clauscarste/quadruped/stl_files/Leg/l1.stl

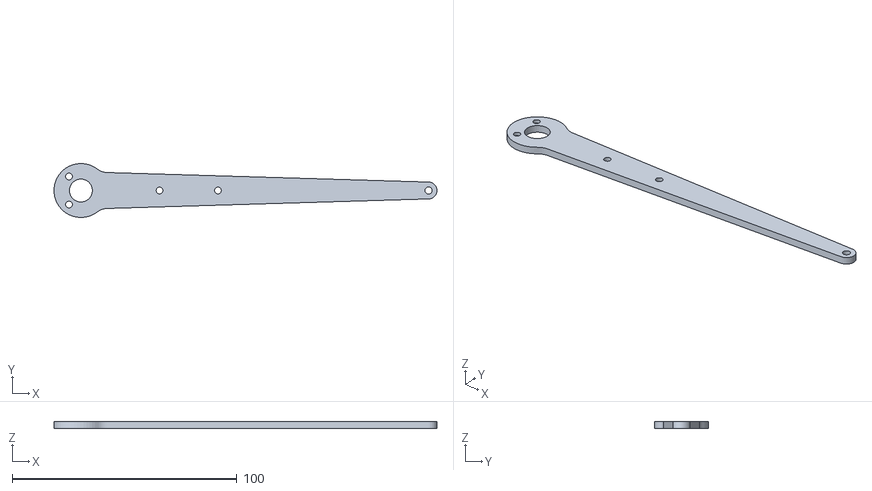
[picture p14: CAD file, 2022-11-11]
stl_files/Leg/l1.stl
170.5 x 24.0 x 3.00
