clauscarste/quadruped/stl_files/Main Body/m5.stl

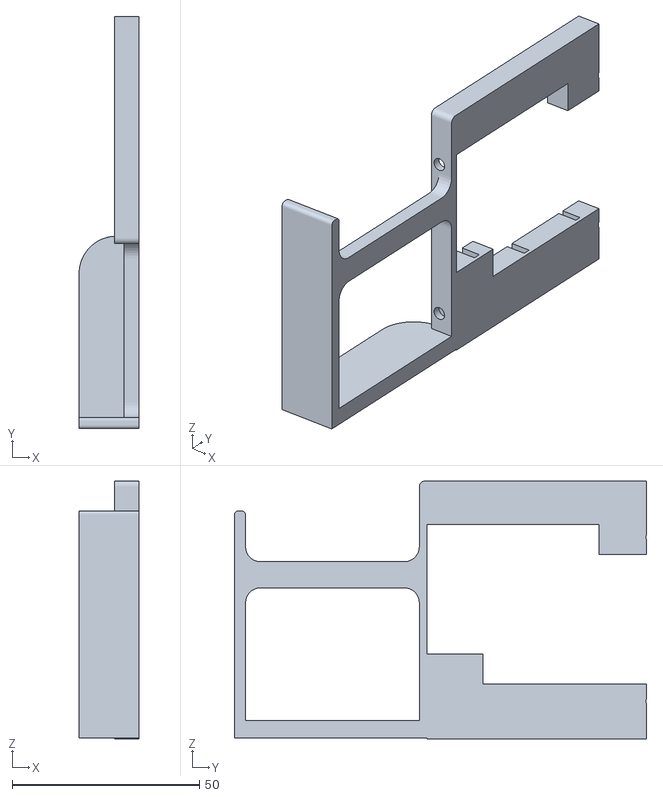
[picture p15: CAD file, 2022-11-11]
stl_files/Main Body/m5.stl
16.0 x 110.1 x 68.9
