clauscarste/quadruped/stl_files/Spine/s10.stl

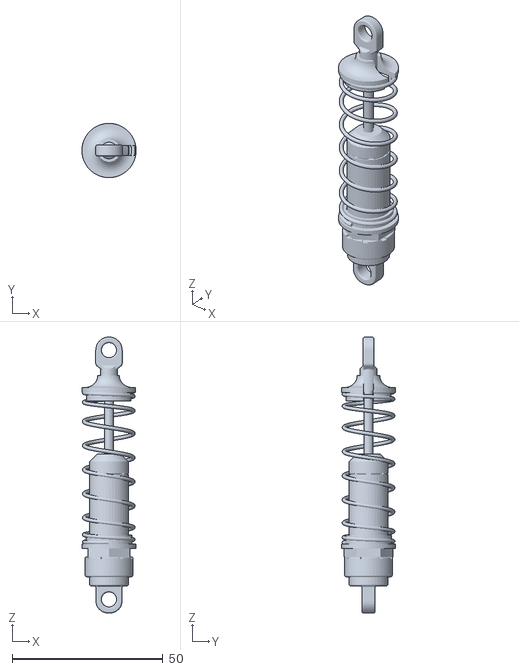
[picture p16: CAD file, 2022-11-11]
stl_files/Spine/s10.stl
18.0 x 18.0 x 91.5
