clauscarste/quadruped/control and simulation/simulation_files/simulation_test/full_quadruped_simulation_pos_control/meshes/lower_leg.stl

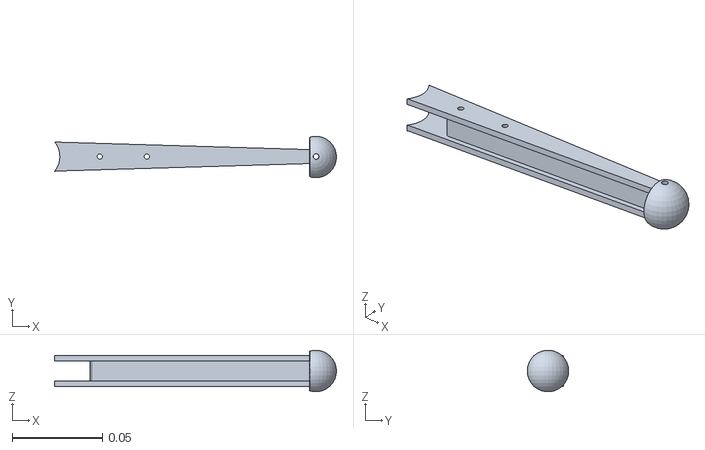
[picture p17: CAD file, 2023-01-09]
control and simulation/simulation_files/simulation_test/full_quadruped_simulation_pos_control/meshes/lower_leg.stl
0.156 x 0.023 x 0.0229
