clauscarste/quadruped/control and simulation/simulation_files/simulation_test/leg_only_simplided copy/meshes2/gearbox_1.stl

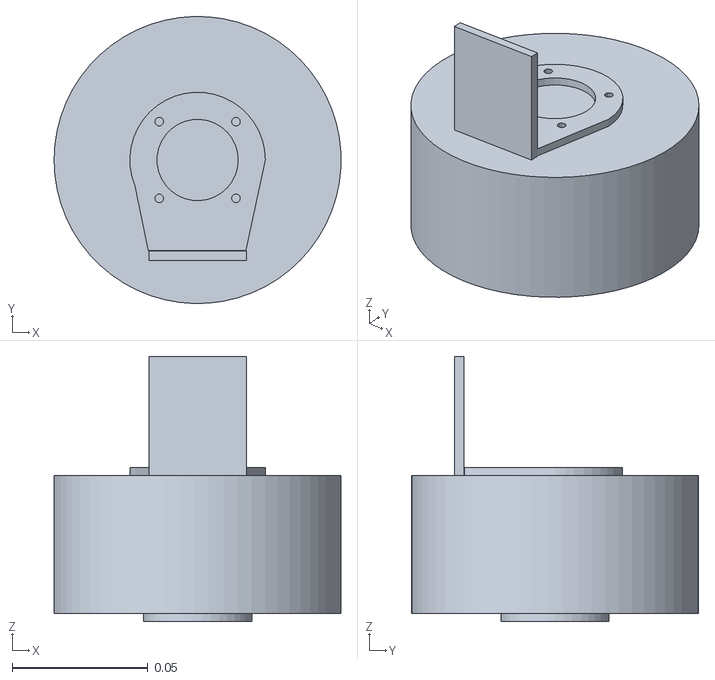
[picture p18: CAD file, 2023-01-24]
control and simulation/simulation_files/simulation_test/leg_only_simplided copy/meshes2/gearbox_1.stl
0.106 x 0.106 x 0.0978
