clauscarste/quadruped/stl_files/Gearbox/g8.stl

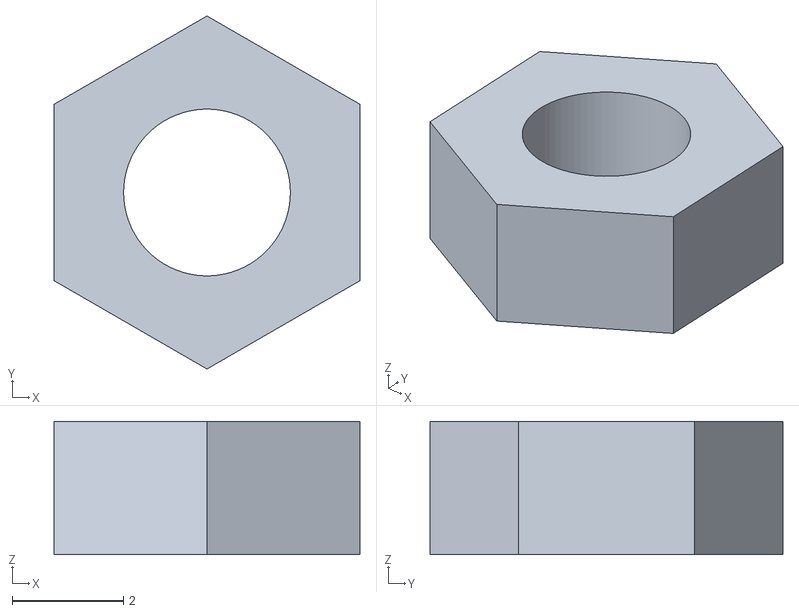
[picture p19: CAD file, 2022-11-11]
stl_files/Gearbox/g8.stl
5.50 x 6.35 x 2.40
