clauscarste/quadruped/stl_files/Main Body/m15.stl

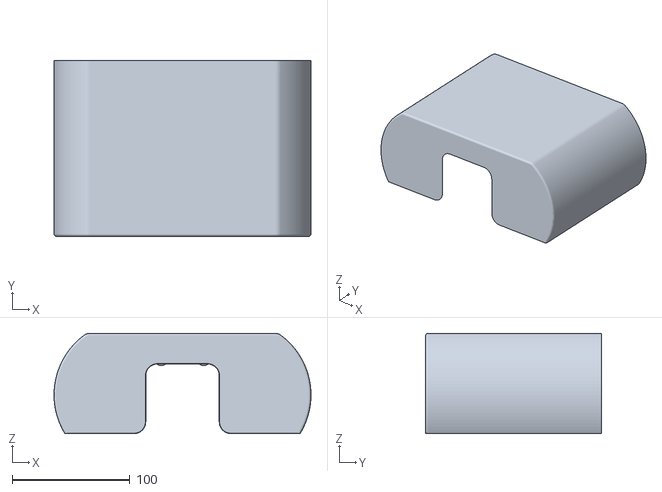
[picture p20: CAD file, 2022-11-11]
stl_files/Main Body/m15.stl
217.9 x 149.0 x 85.1
