clauscarste/quadruped/stl_files/Spine/s2.stl

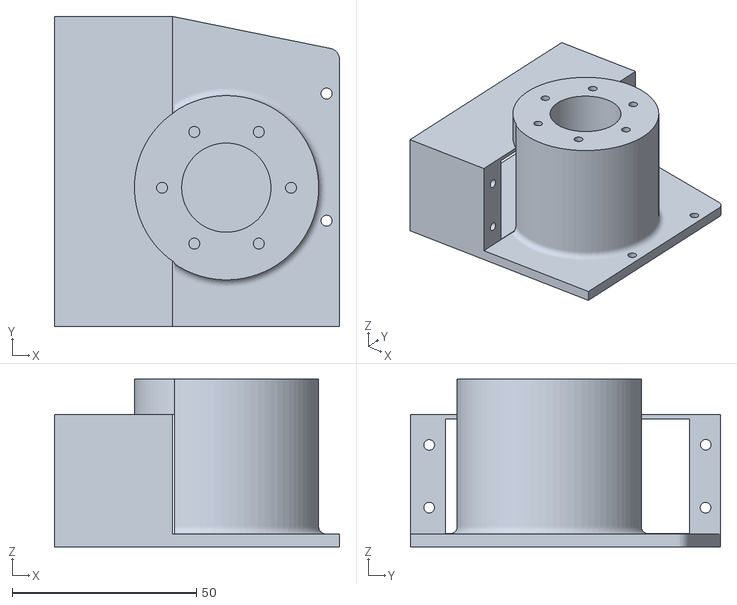
[picture p21: CAD file, 2022-11-11]
stl_files/Spine/s2.stl
77.3 x 84.2 x 45.5
