clauscarste/quadruped/control and simulation/simulation_files/simulation_test/full_quadruped_simulation_pos_control/meshes/case1.stl

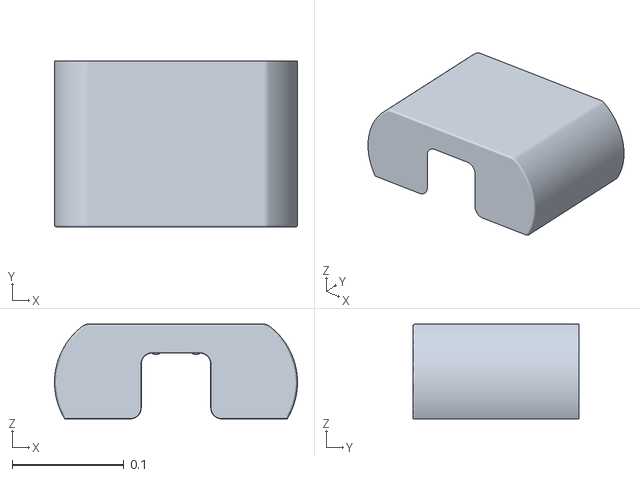
[picture p22: CAD file, 2022-11-25]
control and simulation/simulation_files/simulation_test/full_quadruped_simulation_pos_control/meshes/case1.stl
0.218 x 0.149 x 0.0851
