clauscarste/quadruped/stl_files/Gearbox/g6.stl

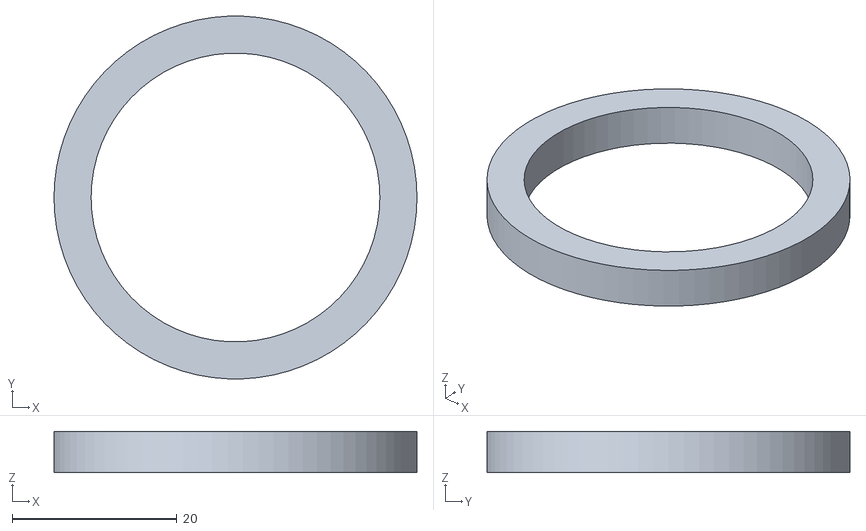
[picture p23: CAD file, 2022-11-11]
stl_files/Gearbox/g6.stl
44.0 x 44.0 x 5.00
