clauscarste/quadruped/stl_files/Leg/s4.stl

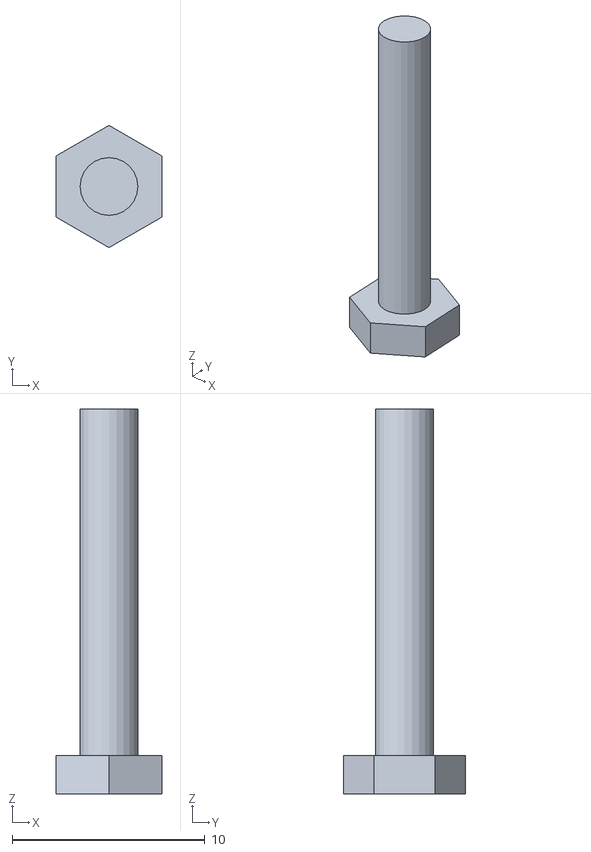
[picture p24: CAD file, 2022-11-11]
stl_files/Leg/s4.stl
5.50 x 6.35 x 20.0
