clauscarste/quadruped/stl_files/Main Body/m2.stl

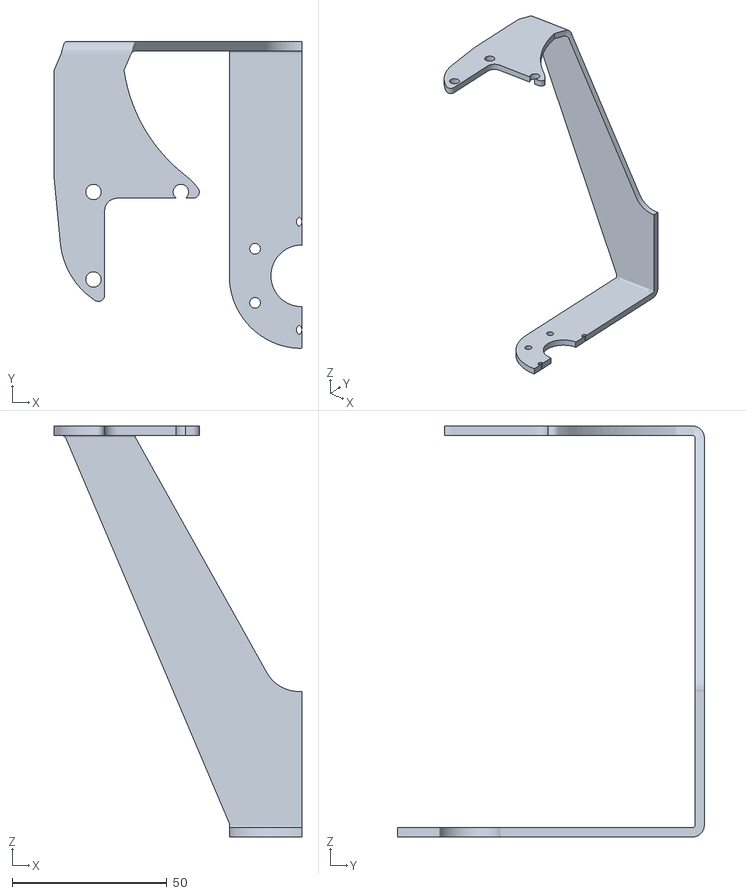
[picture p25: CAD file, 2022-11-11]
stl_files/Main Body/m2.stl
80.2 x 99.3 x 133.0
