clauscarste/quadruped/stl_files/Spine/s1.stl

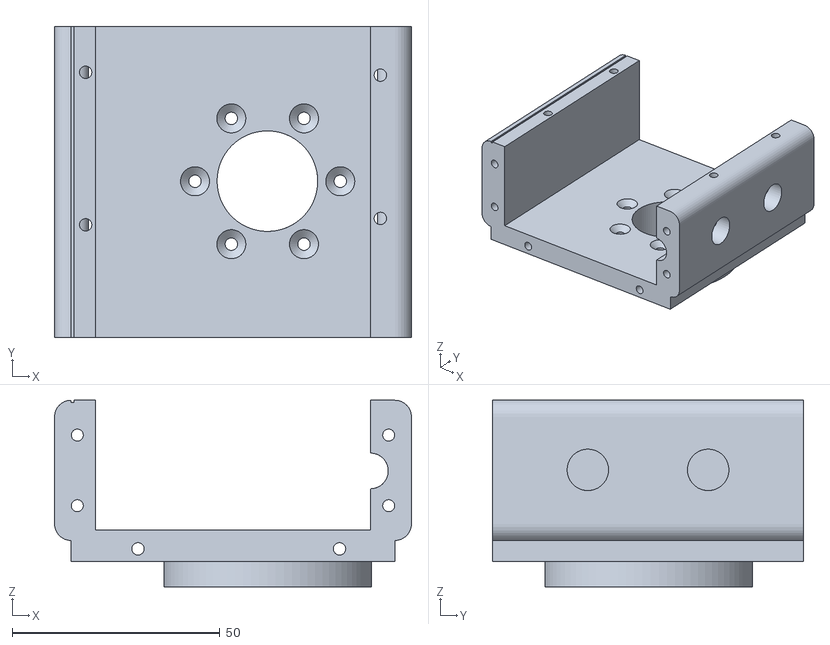
[picture p26: CAD file, 2022-11-11]
stl_files/Spine/s1.stl
86.0 x 75.0 x 44.9
