clauscarste/quadruped/control and simulation/simulation_files/simulation_test/full_quadruped_simulation_pos_control/meshes/case2.stl

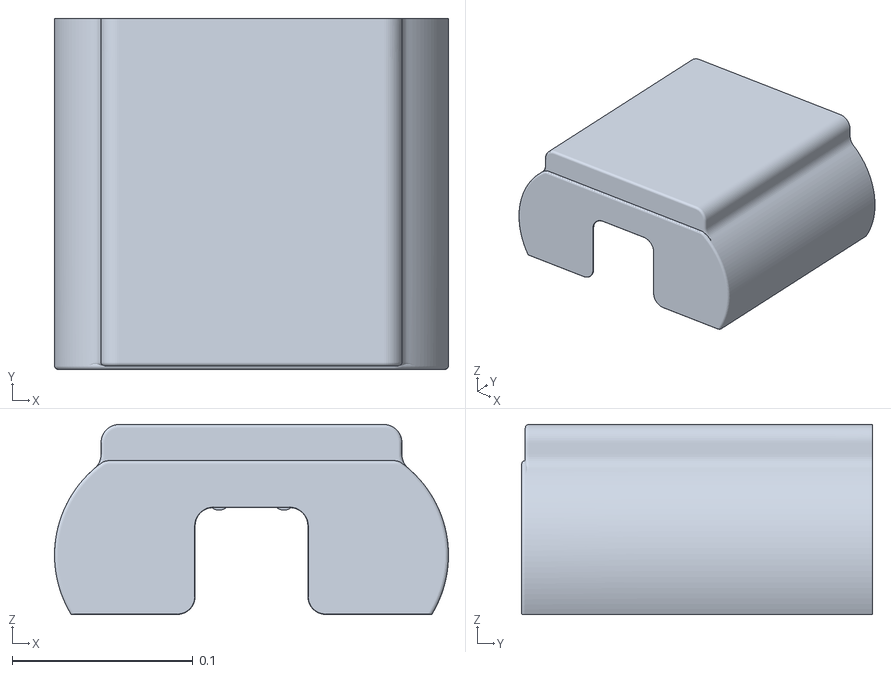
[picture p27: CAD file, 2022-11-25]
control and simulation/simulation_files/simulation_test/full_quadruped_simulation_pos_control/meshes/case2.stl
0.218 x 0.194 x 0.105
