clauscarste/quadruped/control and simulation/simulation_files/simulation_test/leg_only_simplided copy/meshes2/upper_leg.stl

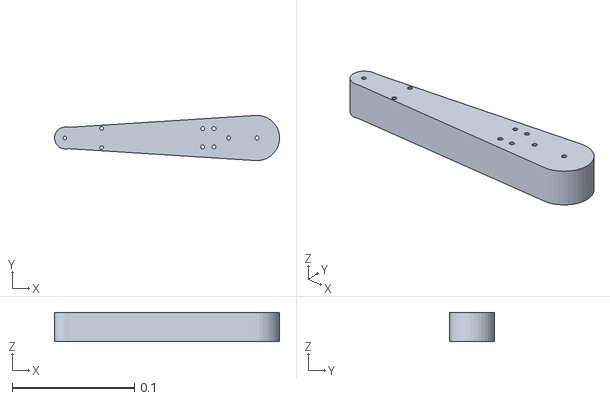
[picture p28: CAD file, 2023-01-24]
control and simulation/simulation_files/simulation_test/leg_only_simplided copy/meshes2/upper_leg.stl
0.184 x 0.0369 x 0.024
