clauscarste/quadruped/stl_files/Gearbox/g7.stl

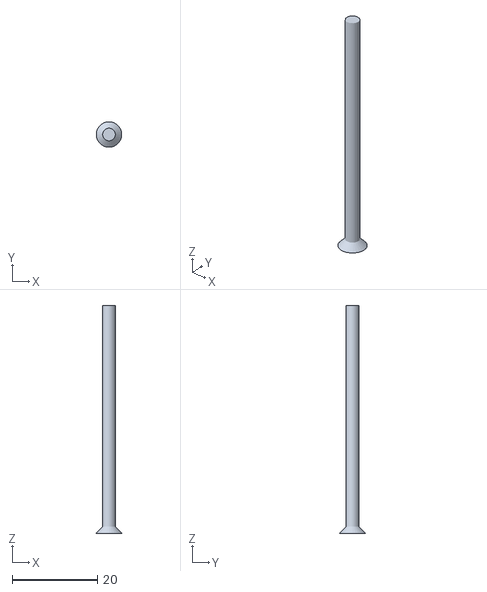
[picture p29: CAD file, 2022-11-11]
stl_files/Gearbox/g7.stl
6.00 x 6.00 x 53.6
