clauscarste/quadruped/stl_files/Leg/l3.stl

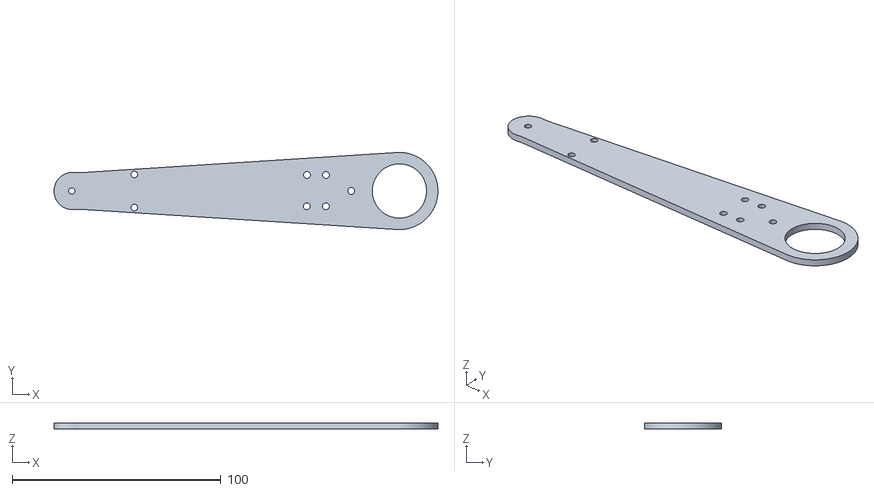
[picture p30: CAD file, 2022-11-11]
stl_files/Leg/l3.stl
184.1 x 37.0 x 3.00
