clauscarste/quadruped/stl_files/Main Body/m16.stl

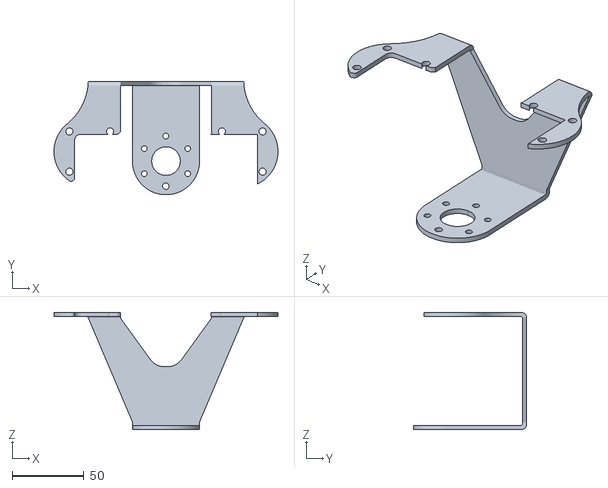
[picture p31: CAD file, 2022-11-11]
stl_files/Main Body/m16.stl
156.6 x 79.3 x 81.9
