clauscarste/quadruped/stl_files/Spine/s9.stl

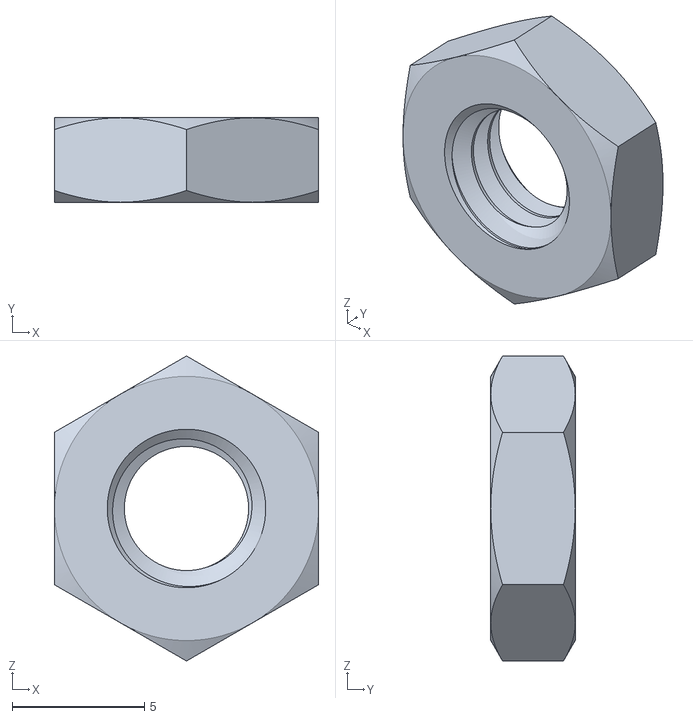
[picture p32: CAD file, 2022-11-11]
stl_files/Spine/s9.stl
10.0 x 3.20 x 11.5
