clauscarste/quadruped/control and simulation/simulation_files/simulation_test/full_quadruped_simulation_pos_control/meshes/front_alu_3.stl

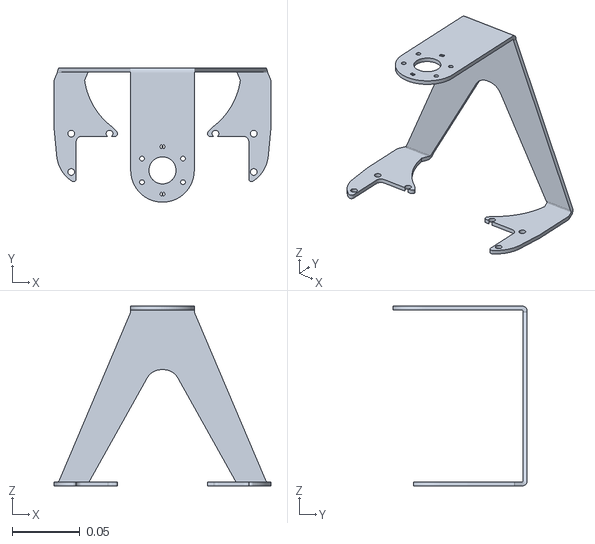
[picture p33: CAD file, 2022-11-15]
control and simulation/simulation_files/simulation_test/full_quadruped_simulation_pos_control/meshes/front_alu_3.stl
0.16 x 0.0993 x 0.133
