clauscarste/quadruped/control and simulation/simulation_files/simulation_test/leg_only_simplided copy/meshes/front_alu_1.stl

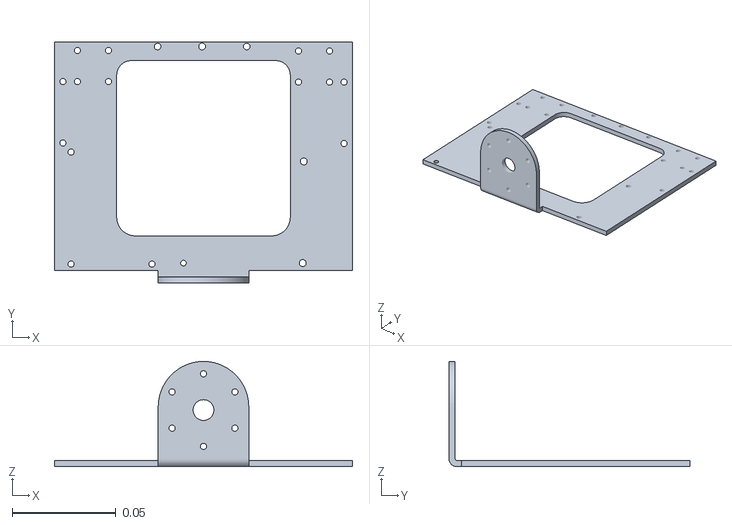
[picture p34: CAD file, 2022-11-15]
control and simulation/simulation_files/simulation_test/leg_only_simplided copy/meshes/front_alu_1.stl
0.144 x 0.116 x 0.0508
