clauscarste/quadruped/control and simulation/simulation_files/simulation_test/leg_only_simplided copy/meshes2/gearbox2.stl

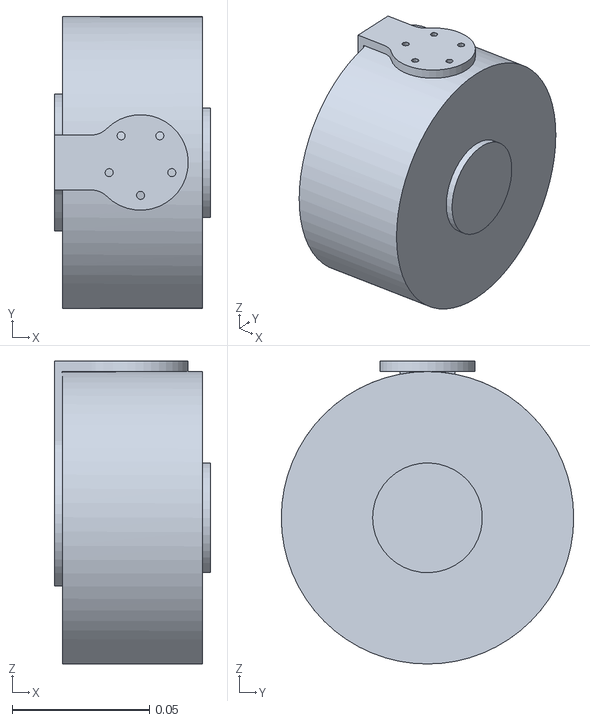
[picture p35: CAD file, 2023-01-24]
control and simulation/simulation_files/simulation_test/leg_only_simplided copy/meshes2/gearbox2.stl
0.0569 x 0.107 x 0.11
