clauscarste/quadruped/stl_files/Gearbox/g5.stl

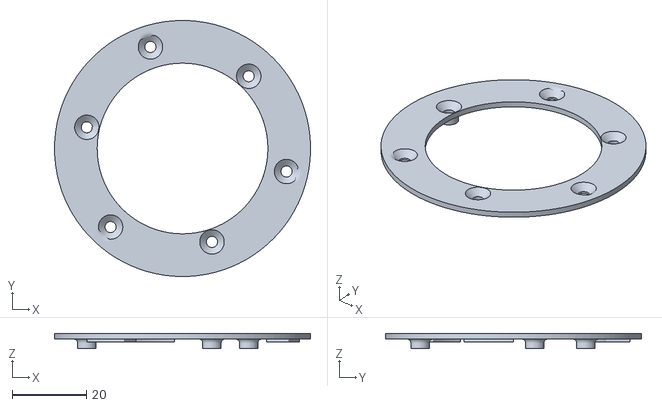
[picture p36: CAD file, 2022-11-11]
stl_files/Gearbox/g5.stl
69.0 x 69.0 x 4.00
