clauscarste/quadruped/stl_files/Leg/l2.stl

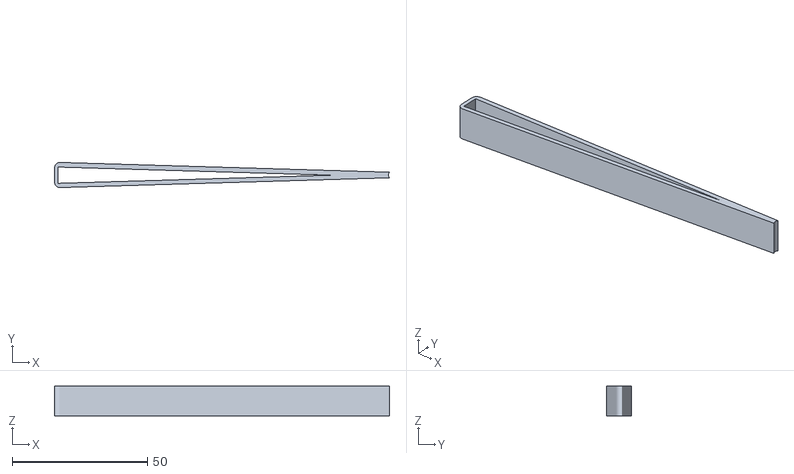
[picture p37: CAD file, 2022-11-11]
stl_files/Leg/l2.stl
124.1 x 9.31 x 11.0
