clauscarste/quadruped/stl_files/Main Body/m10.stl

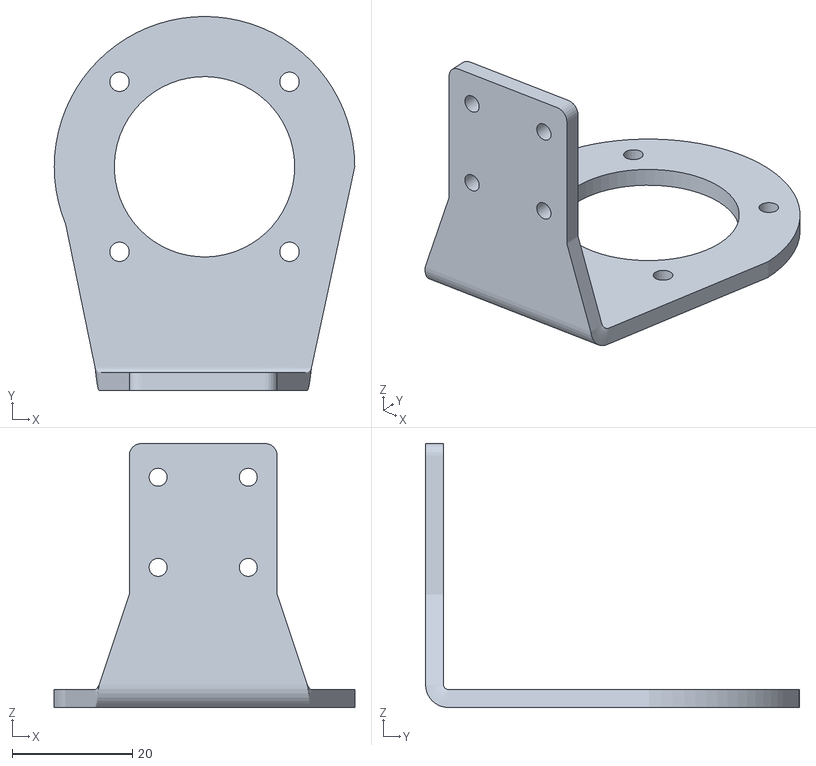
[picture p38: CAD file, 2022-11-11]
stl_files/Main Body/m10.stl
50.0 x 62.2 x 43.9
