clauscarste/quadruped/stl_files/Spine/s8.stl

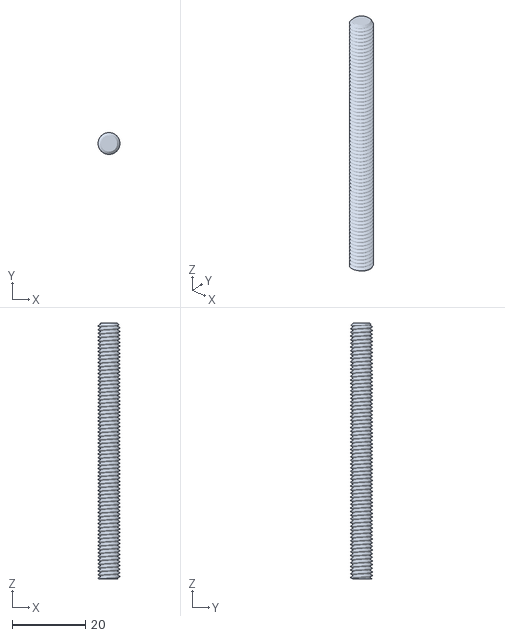
[picture p39: CAD file, 2022-11-11]
stl_files/Spine/s8.stl
6.00 x 6.00 x 70.0
