clauscarste/quadruped/control and simulation/simulation_files/simulation_test/full_quadruped_simulation_pos_control/meshes/upper_leg.stl

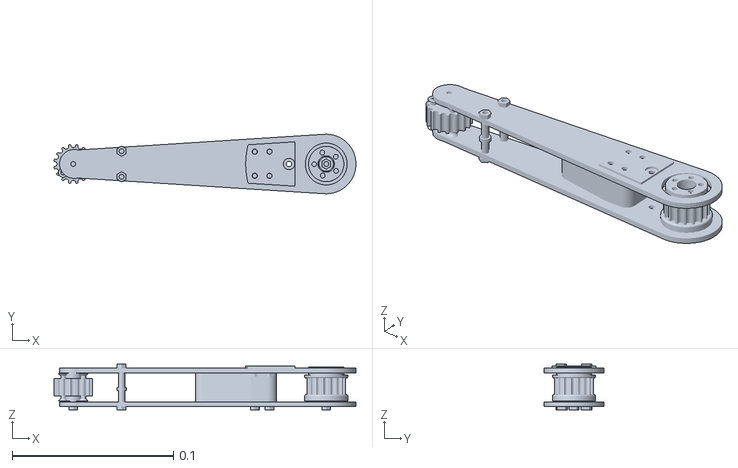
[picture p40: CAD file, 2022-11-15]
control and simulation/simulation_files/simulation_test/full_quadruped_simulation_pos_control/meshes/upper_leg.stl
0.188 x 0.037 x 0.0285
