clauscarste/quadruped/control and simulation/simulation_files/simulation_test/leg_only_simplided copy/meshes/encoder.stl

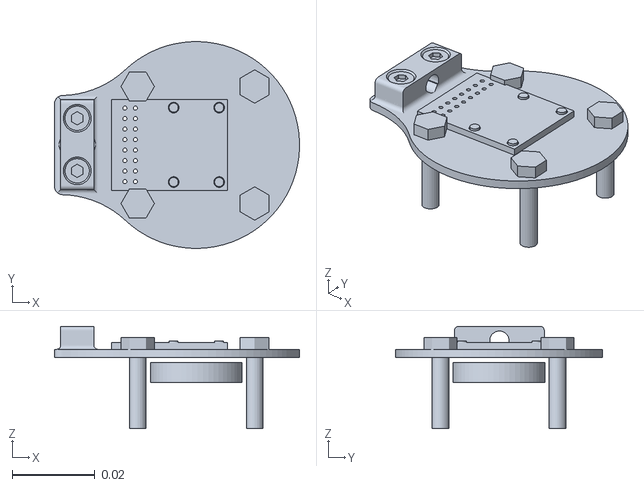
[picture p41: CAD file, 2022-11-15]
control and simulation/simulation_files/simulation_test/leg_only_simplided copy/meshes/encoder.stl
0.0592 x 0.05 x 0.0248
