clauscarste/quadruped/stl_files/Gearbox/g2.stl

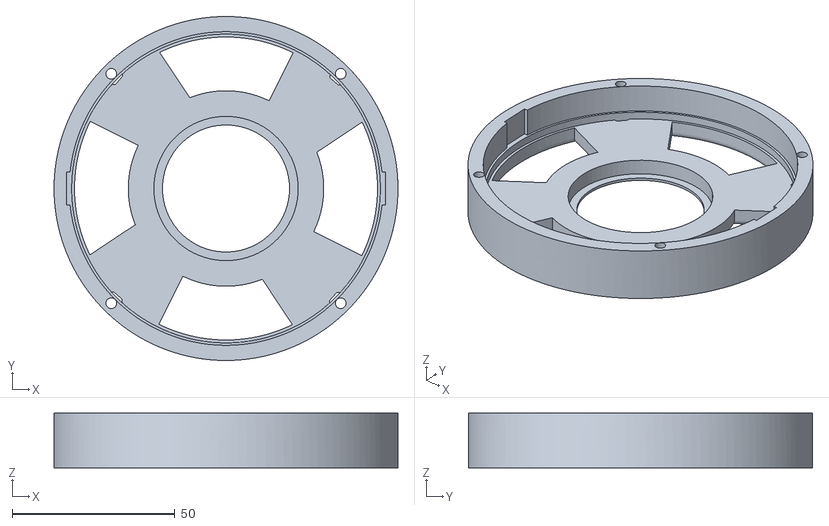
[picture p42: CAD file, 2022-11-11]
stl_files/Gearbox/g2.stl
105.6 x 105.6 x 16.8
