clauscarste/quadruped/stl_files/Leg/l8.stl

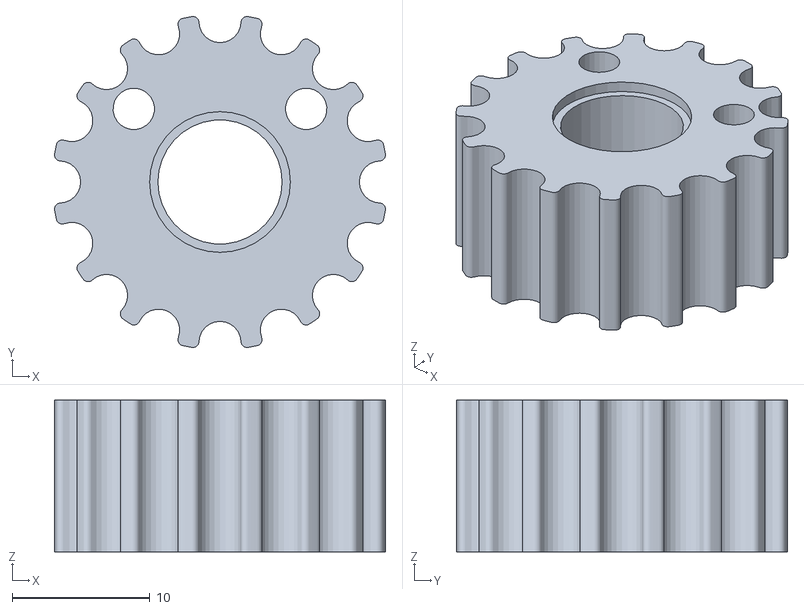
[picture p43: CAD file, 2022-11-11]
stl_files/Leg/l8.stl
24.0 x 24.0 x 11.0
