clauscarste/quadruped/stl_files/Spine/s7.stl

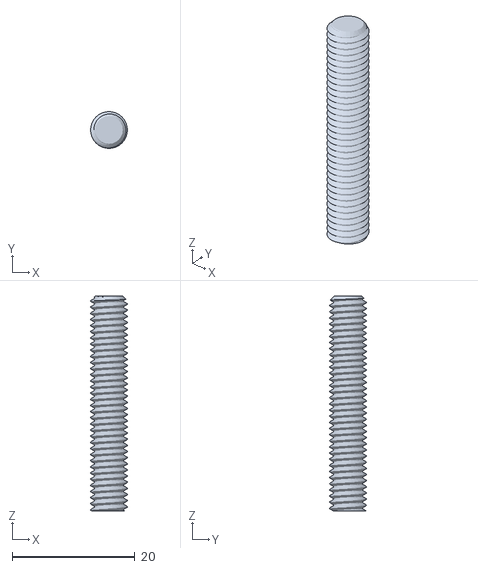
[picture p44: CAD file, 2022-11-11]
stl_files/Spine/s7.stl
6.00 x 6.00 x 35.0
