clauscarste/quadruped/control and simulation/simulation_files/simulation_test/full_quadruped_simulation_pos_control/meshes/spacer_spine.stl

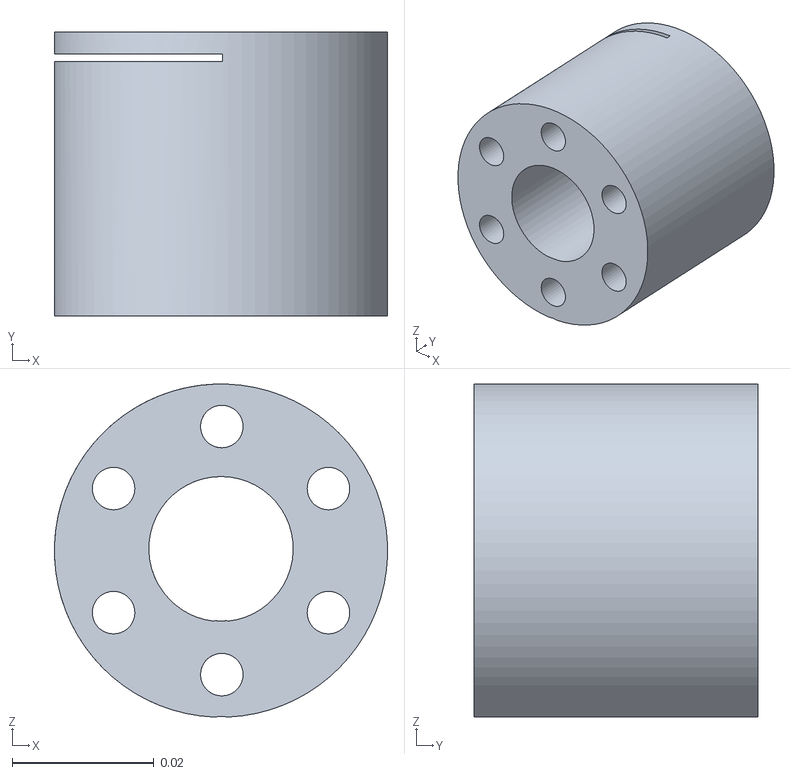
[picture p45: CAD file, 2022-11-15]
control and simulation/simulation_files/simulation_test/full_quadruped_simulation_pos_control/meshes/spacer_spine.stl
0.047 x 0.04 x 0.047
