clauscarste/quadruped/control and simulation/simulation_files/simulation_test/leg_only_simplided copy/meshes/back_alu_1.stl

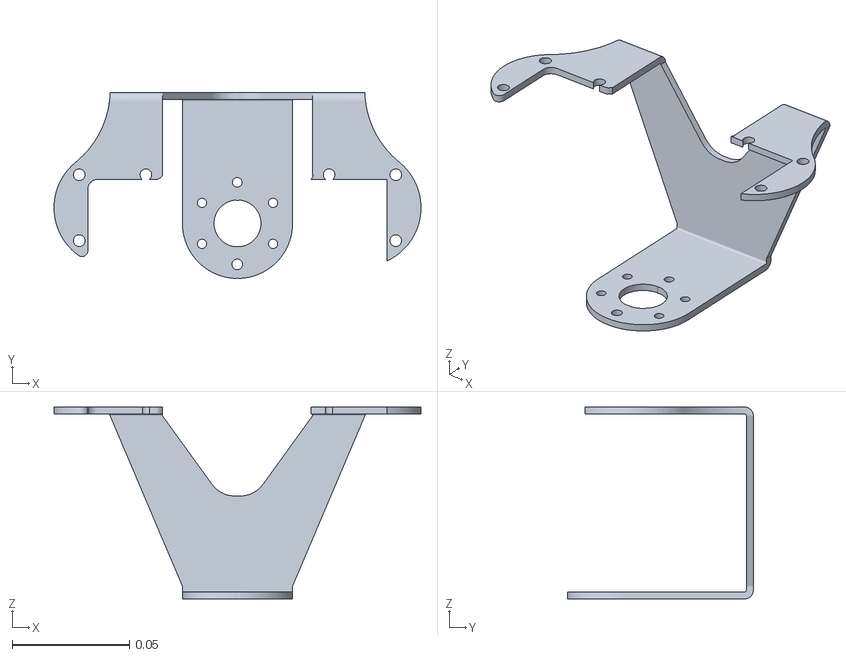
[picture p46: CAD file, 2022-11-15]
control and simulation/simulation_files/simulation_test/leg_only_simplided copy/meshes/back_alu_1.stl
0.157 x 0.0793 x 0.0819
