clauscarste/quadruped/stl_files/Gearbox/g4.stl

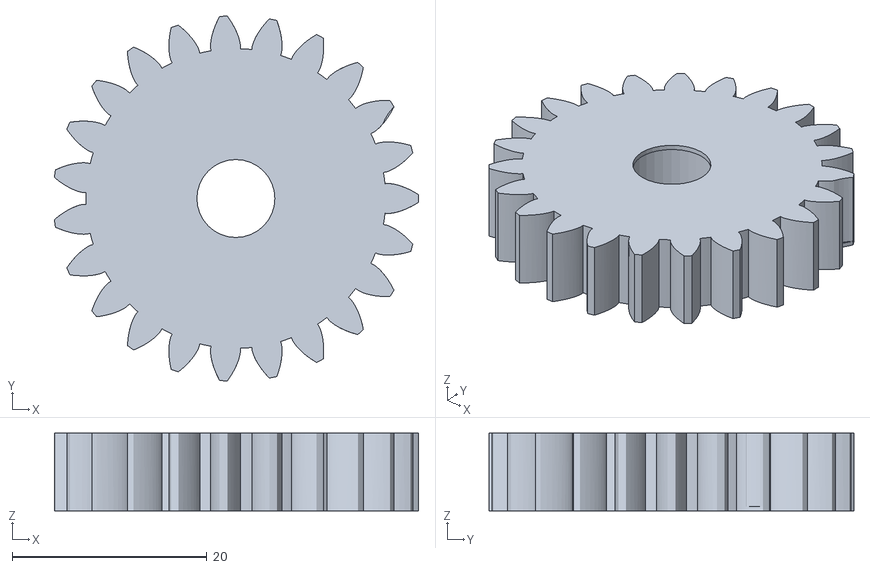
[picture p47: CAD file, 2022-11-11]
stl_files/Gearbox/g4.stl
37.4 x 37.5 x 8.00
