clauscarste/quadruped/stl_files/Leg/s2.stl

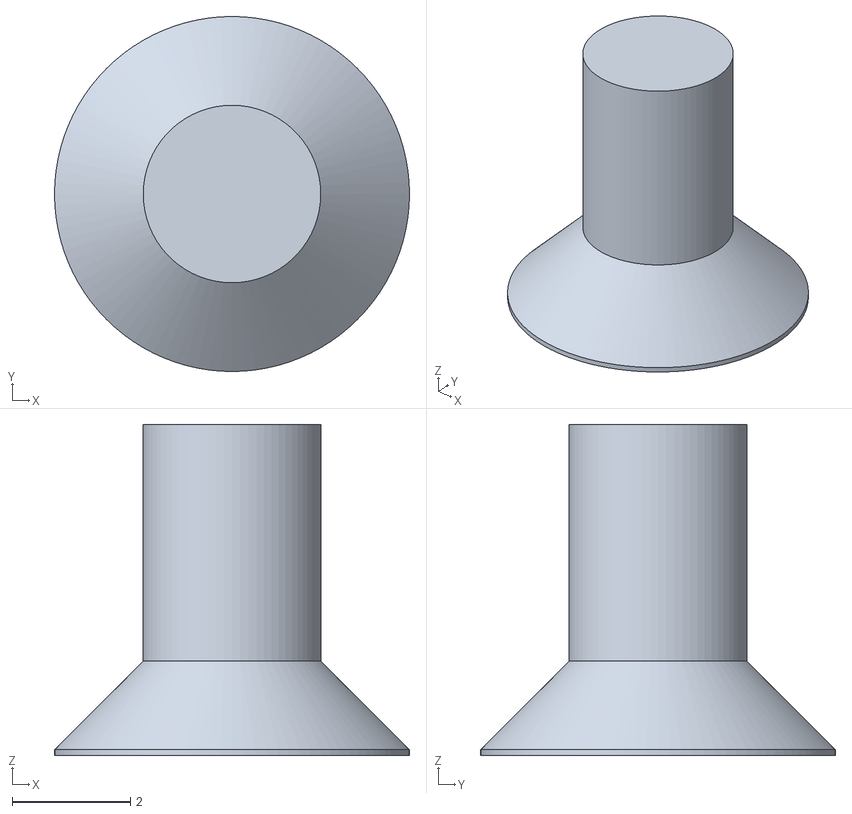
[picture p48: CAD file, 2022-11-11]
stl_files/Leg/s2.stl
6.00 x 6.00 x 5.60
