clauscarste/quadruped/stl_files/Main Body/m17.stl

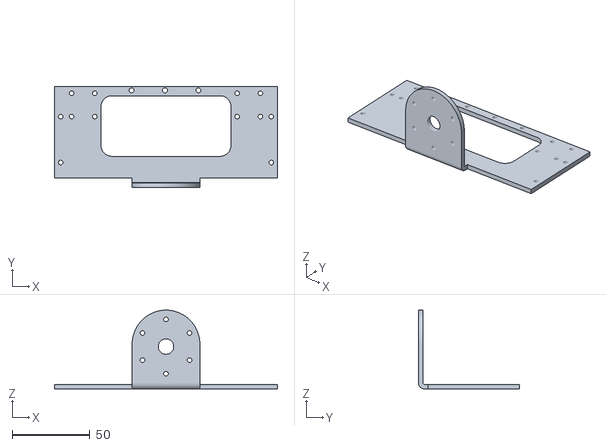
[picture p49: CAD file, 2022-11-11]
stl_files/Main Body/m17.stl
143.7 x 65.1 x 50.8
