clauscarste/quadruped/stl_files/Spine/s11.stl

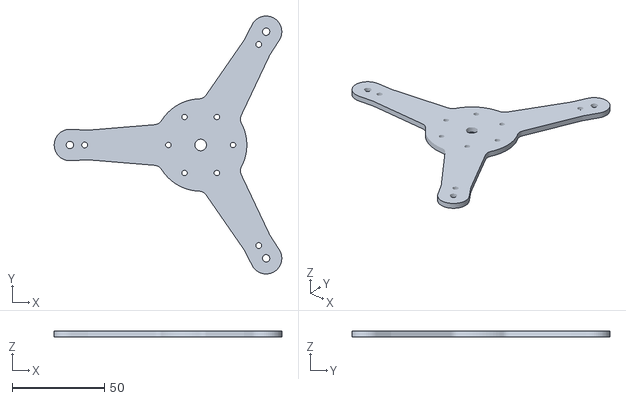
[picture p50: CAD file, 2022-11-11]
stl_files/Spine/s11.stl
123.3 x 139.7 x 3.00
