clauscarste/quadruped/control and simulation/simulation_files/simulation_test/leg_only_simplided copy/meshes/upper_leg_belt.stl

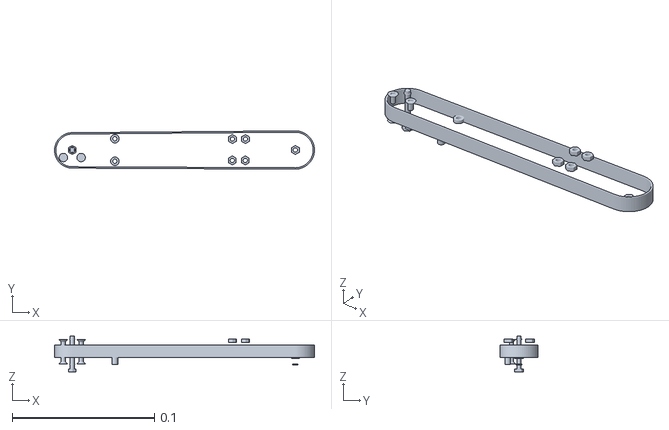
[picture p51: CAD file, 2022-11-15]
control and simulation/simulation_files/simulation_test/leg_only_simplided copy/meshes/upper_leg_belt.stl
0.183 x 0.027 x 0.025
