clauscarste/quadruped/stl_files/Gearbox/g3.stl

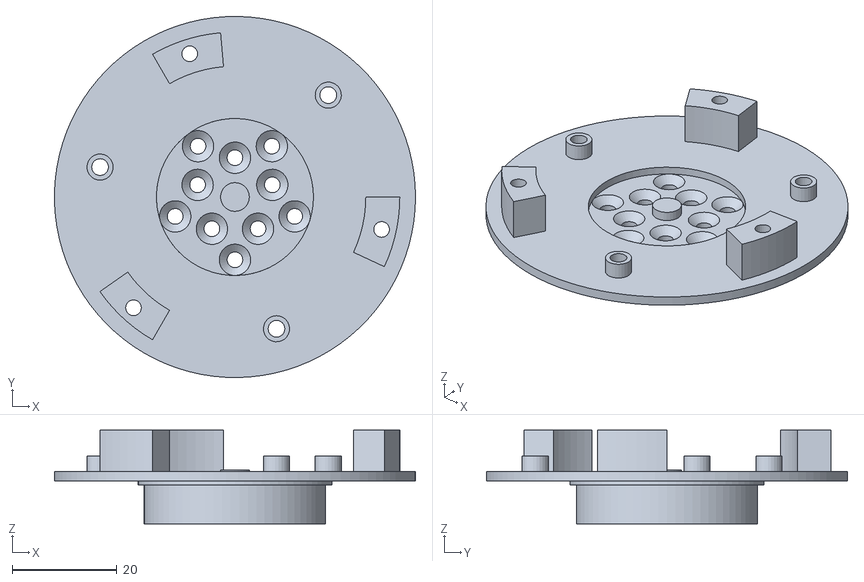
[picture p52: CAD file, 2022-11-11]
stl_files/Gearbox/g3.stl
69.0 x 69.0 x 17.9
