clauscarste/quadruped/stl_files/Leg/s3.stl

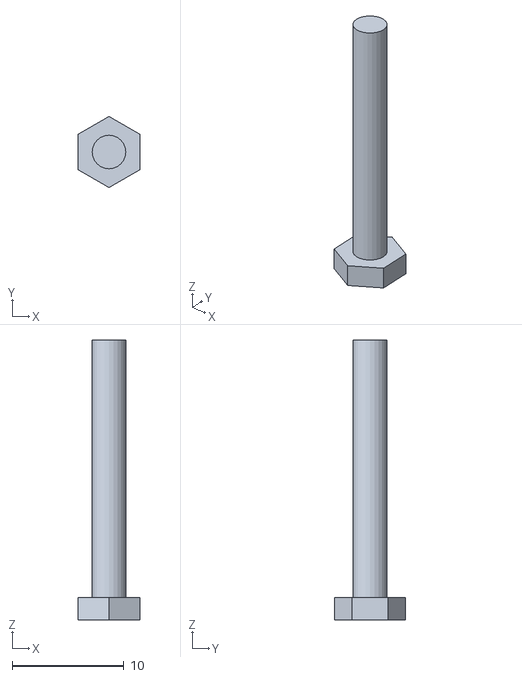
[picture p53: CAD file, 2022-11-11]
stl_files/Leg/s3.stl
5.50 x 6.35 x 25.0
