clauscarste/quadruped/stl_files/Main Body/m7.stl

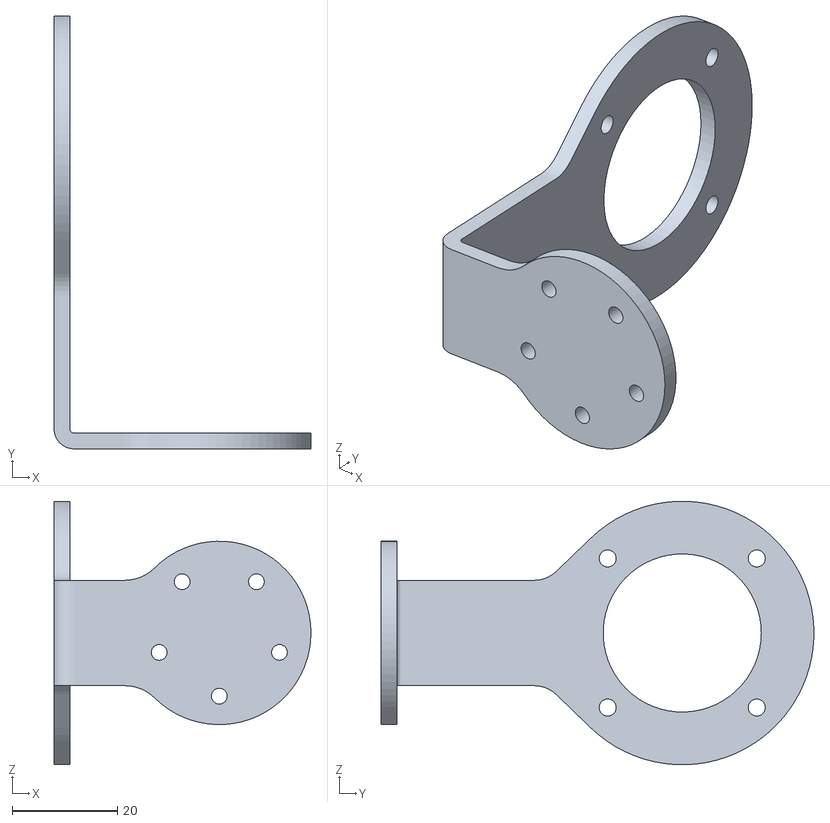
[picture p54: CAD file, 2022-11-11]
stl_files/Main Body/m7.stl
48.8 x 82.1 x 50.0
