clauscarste/quadruped/stl_files/Spine/s6.stl

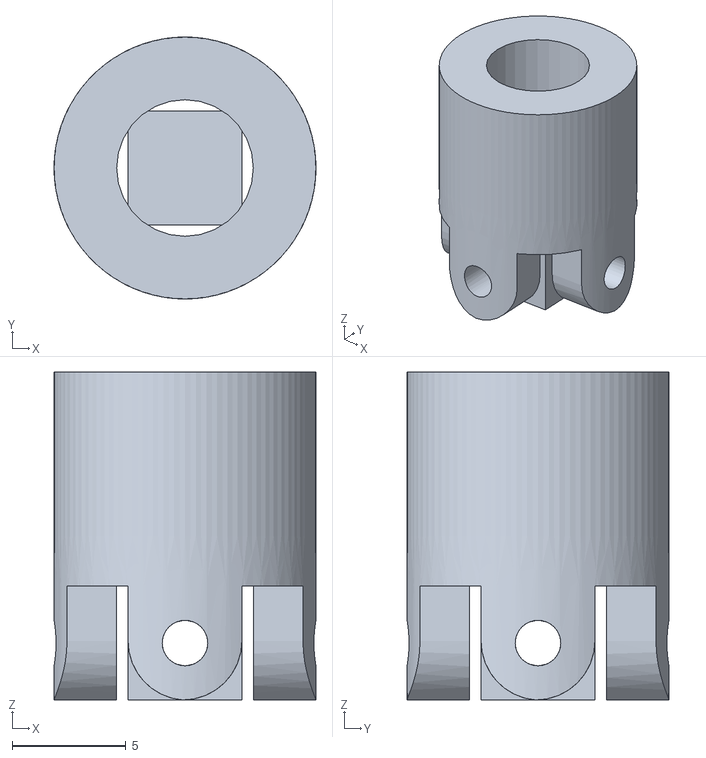
[picture p55: CAD file, 2022-11-11]
stl_files/Spine/s6.stl
11.5 x 11.5 x 14.4
