clauscarste/quadruped/control and simulation/simulation_files/simulation_test/full_quadruped_simulation_pos_control/meshes/back_alu_2.stl

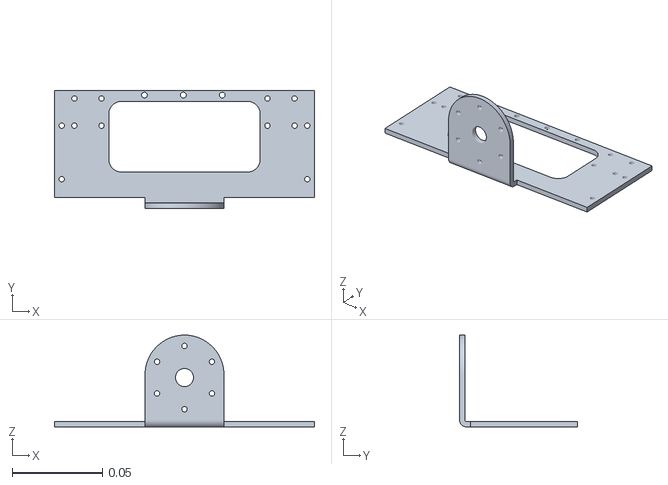
[picture p56: CAD file, 2022-11-15]
control and simulation/simulation_files/simulation_test/full_quadruped_simulation_pos_control/meshes/back_alu_2.stl
0.144 x 0.0651 x 0.0508
