clauscarste/quadruped/control and simulation/simulation_files/simulation_test/leg_only_simplided copy/meshes2/battery.stl

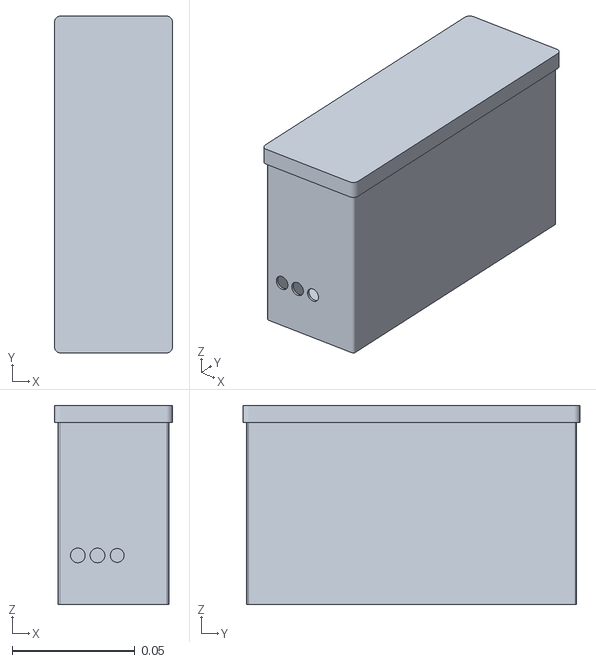
[picture p57: CAD file, 2022-11-15]
control and simulation/simulation_files/simulation_test/leg_only_simplided copy/meshes2/battery.stl
0.048 x 0.137 x 0.081
