clauscarste/quadruped/stl_files/Leg/l7.stl

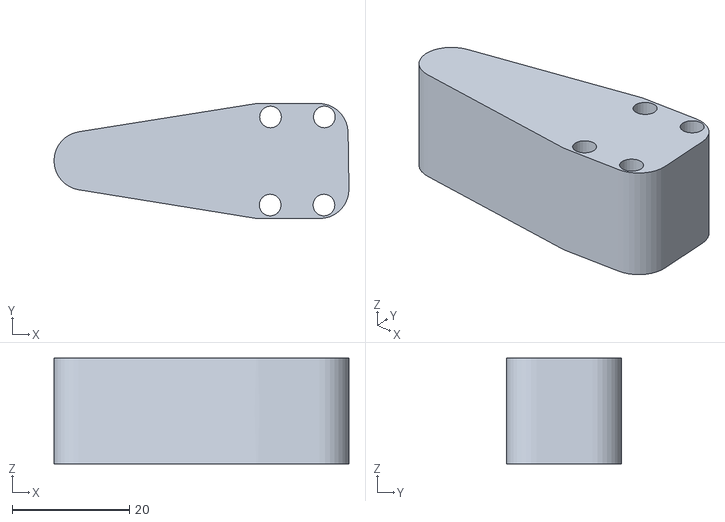
[picture p58: CAD file, 2022-11-11]
stl_files/Leg/l7.stl
50.2 x 19.6 x 18.0
