clauscarste/quadruped/stl_files/Main Body/m1.stl

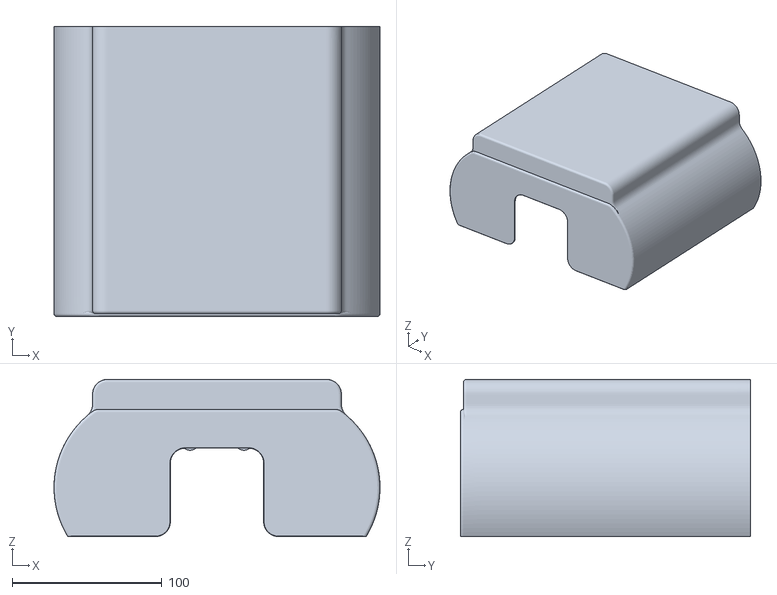
[picture p59: CAD file, 2022-11-11]
stl_files/Main Body/m1.stl
217.9 x 194.0 x 105.1
