clauscarste/quadruped/control and simulation/simulation_files/simulation_test/full_quadruped_simulation_pos_control/meshes/gearbox1_spacer.stl

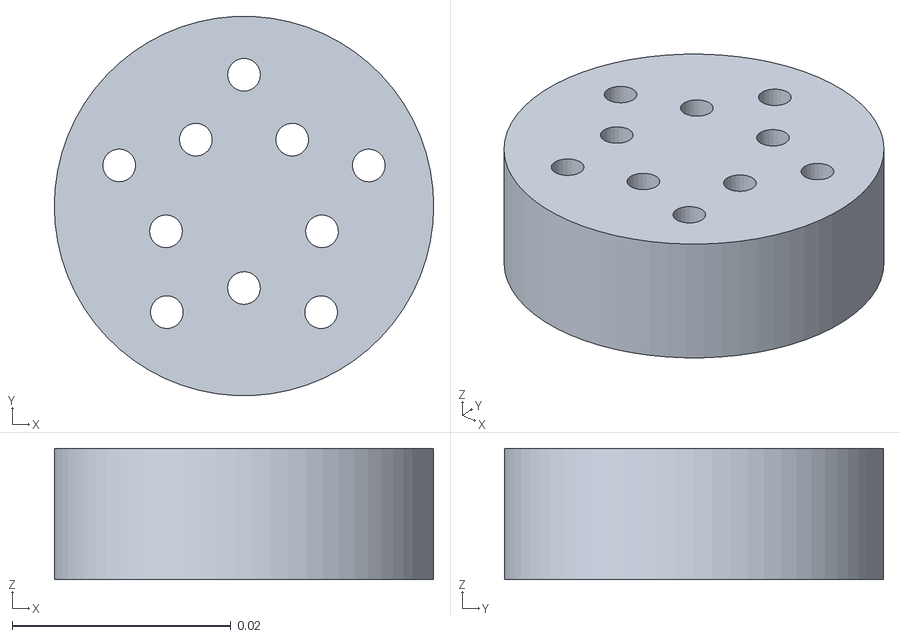
[picture p60: CAD file, 2022-11-15]
control and simulation/simulation_files/simulation_test/full_quadruped_simulation_pos_control/meshes/gearbox1_spacer.stl
0.0347 x 0.0347 x 0.012
