clauscarste/quadruped/stl_files/Gearbox/g12.stl

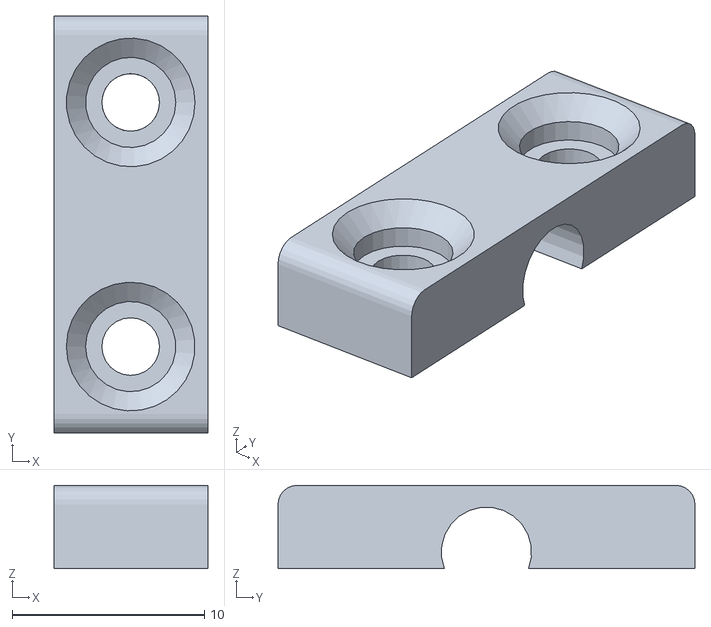
[picture p61: CAD file, 2022-11-11]
stl_files/Gearbox/g12.stl
8.00 x 21.7 x 4.34
