clauscarste/quadruped/stl_files/Leg/l5.stl

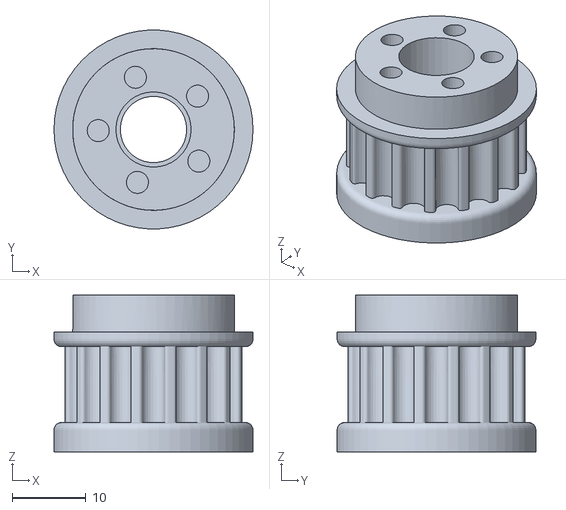
[picture p62: CAD file, 2022-11-11]
stl_files/Leg/l5.stl
27.0 x 27.0 x 21.3
