clauscarste/quadruped/stl_files/Main Body/m13.stl

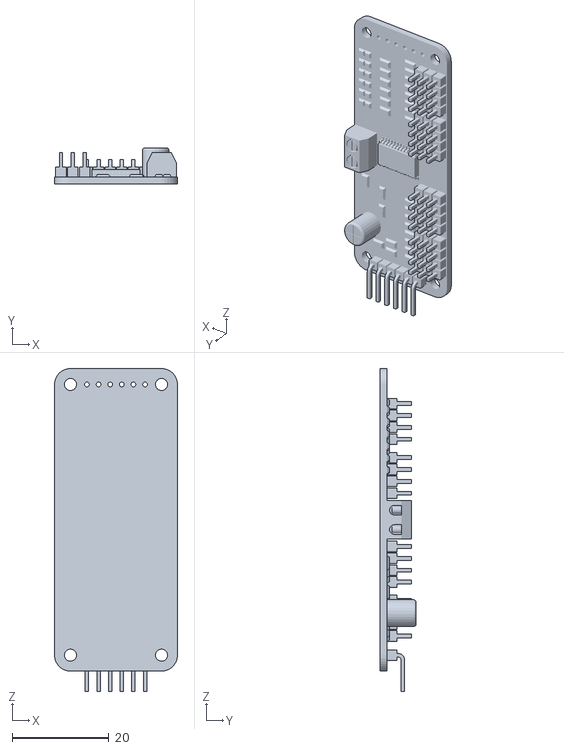
[picture p63: CAD file, 2022-11-11]
stl_files/Main Body/m13.stl
25.4 x 7.51 x 66.7
