clauscarste/quadruped/stl_files/Gearbox/g1.stl

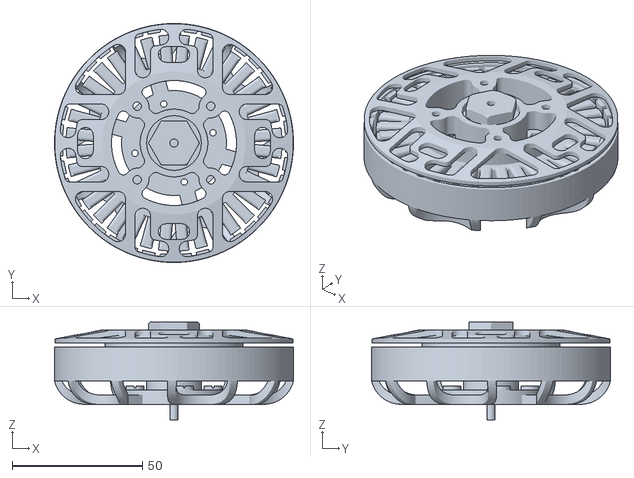
[picture p64: CAD file, 2022-11-11]
stl_files/Gearbox/g1.stl
91.8 x 91.8 x 37.6
