clauscarste/quadruped/stl_files/Leg/l9.stl

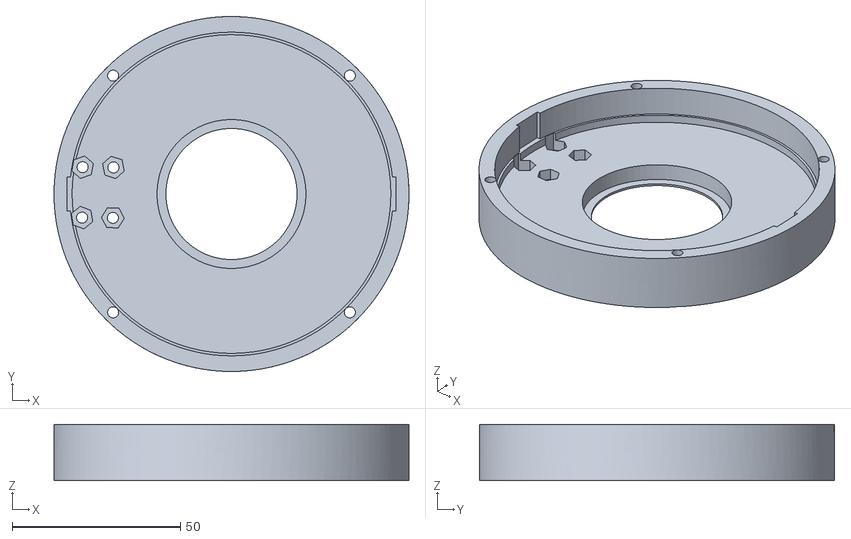
[picture p65: CAD file, 2022-11-11]
stl_files/Leg/l9.stl
105.6 x 105.6 x 16.8
