clauscarste/quadruped/stl_files/Main Body/m12.stl

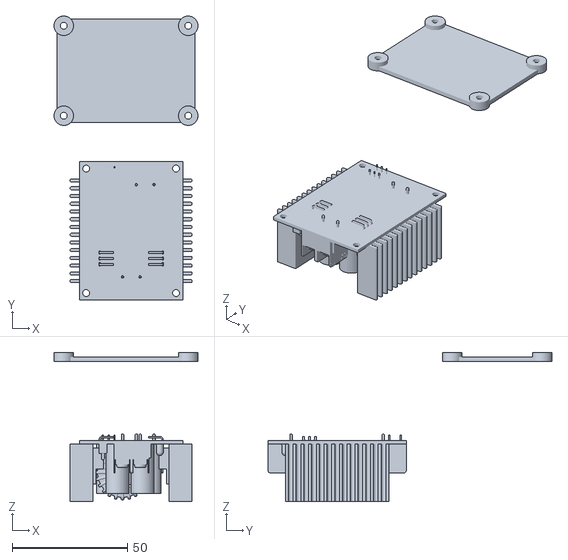
[picture p66: CAD file, 2022-11-11]
stl_files/Main Body/m12.stl
62.5 x 123.2 x 64.9
