clauscarste/quadruped/stl_files/Leg/l10.stl

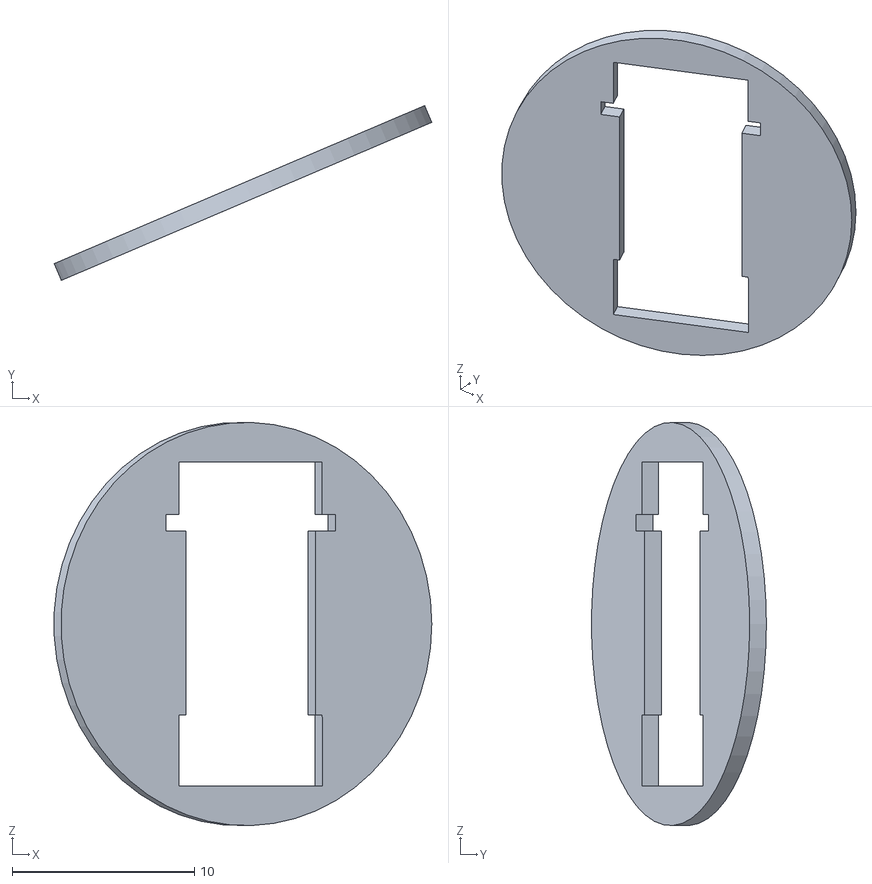
[picture p67: CAD file, 2022-11-11]
stl_files/Leg/l10.stl
20.7 x 9.60 x 22.1
