clauscarste/quadruped/stl_files/Leg/l6.stl

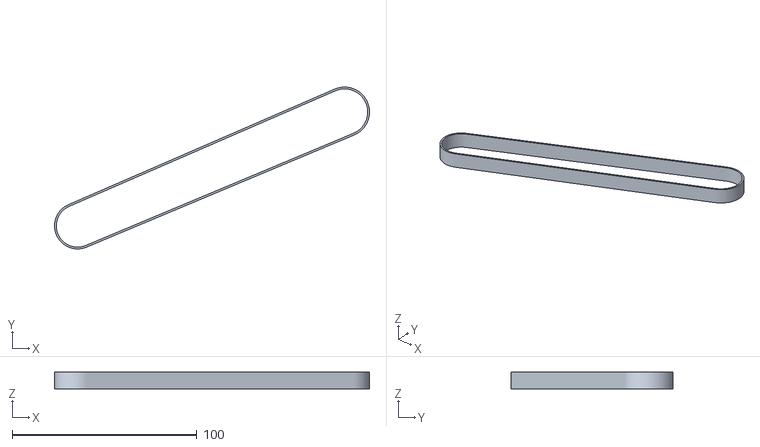
[picture p68: CAD file, 2022-11-11]
stl_files/Leg/l6.stl
170.5 x 87.6 x 9.00
